werner-rh/drybox-control/WRKeyStateDef.h

/***
 *  WRKeyStateDef.h 
 *  Contains constant definitons and Prototypes 
 */

#ifndef _WRKEYSTATEDEF_H
  #define _WRKEYSTATEDEF_H

#include <Arduino.h>

// Prototypes in other files ----------

uint8_t CheckKeyState(uint8_t * KeyState, uint8_t KeyPin);

#endif
